Hiroki-Goto/ori_keyboard/src/no_use/master/keycode.h

#ifndef KEYCODE_H_
#define KEYCODE_H_

enum {
    KC_NONE = 0x00,

    KC_ENT = 0xB0,
    KC_ESC,
    KC_BSPC,
    KC_TAB,
    KC_CAPS = 0xC1,
    KC_DEL = 0xD4,

    KC_LCTL = 0x80,
    KC_LSFT,
    KC_LALT,
    KC_LGUI,
    KC_RCTL,
    KC_RSFT,
    KC_RALT,
    KC_RGUI,

    KC_A = 0x61,
    KC_B,
    KC_C,
    KC_D,
    KC_E,
    KC_F,
    KC_G,
    KC_H,
    KC_I,
    KC_J,
    KC_K,
    KC_L,
    KC_M,
    KC_N,
    KC_O,
    KC_P,
    KC_Q,
    KC_R,
    KC_S,
    KC_T,
    KC_U,
    KC_V,
    KC_W,
    KC_X,
    KC_Y,
    KC_Z
};

#endif
