Hiroki-Goto/ori_keyboard/src/no_use/slave/param.h

#ifndef PARAM_H_
#define PARAM_H_

#define SLAVE_ID 8
#define MSG_BYTE 1

#define SLAVE_ROW_NUM 1
#define SLAVE_COL_NUM 2

#define SLAVE_ID 8

const int  slave_row_pin[SLAVE_ROW_NUM] = {9};
const int  slave_col_pin[SLAVE_COL_NUM] = {10, 16};


#endif
